sebasdv/redbearpad-pcb/firmware/redbearpad_xinput/redbearpad_xinput.ino

/*
 * RedBearPad v2 - XInput (mando Xbox 360) de 12 botones, sin OLED.
 * Placa de compilacion: "Arduino Micro w/ XInput" (FQBN xinput:avr:micro).
 * Sin serial (XInput no es CDC): LED 13 parpadea como "vivo".
 * Reflasheo: doble-reset manual para entrar al bootloader.
 *
 * Mapeo (contrato PCB v2). PIN_BOTON en orden de indice fisico:
 *   0:Arriba(D3,SW1) 1:Abajo(D1,SW2) 2:Izq(D2,SW3) 3:Der(D0,SW4)
 *   4:SW5(D11) 5:SW6(D12) 6:SW7(A0) 7:SW8(A1)
 *   8:L(D8,SW9) 9:R(D9,SW10) 10:Select(D5,SW11) 11:Start(D10,SW12)
 *
 * Los 4 botones de cara son un cuadrado 2x2 en la mitad derecha de la placa:
 *   SW5 arriba-izq  SW6 arriba-der
 *   SW7 abajo-izq   SW8 abajo-der
 * Se asignan como el diamante Xbox girado 45 grados, de modo que se cumplan las
 * cuatro relaciones de la convencion: Y arriba, A abajo, X izquierda, B derecha.
 *   X Y
 *   A B
 */
#include <XInput.h>

const uint8_t NUM_BOTONES = 12;
const uint8_t PIN_BOTON[NUM_BOTONES] = { 3, 1, 2, 0, 11, 12, A0, A1, 8, 9, 5, 10 };
const uint8_t IDX_UP = 0, IDX_DOWN = 1, IDX_LEFT = 2, IDX_RIGHT = 3;

bool estadoPrev[NUM_BOTONES];
uint8_t integrador[NUM_BOTONES];
uint32_t tUltimoSample = 0;
const uint8_t SAMPLE_MS = 1;
const uint8_t INTEGRADOR_MAX = 12;

void setup() {
  // --- TEST OVERCLOCK: baja el CPU a 8 MHz (en spec) sin tocar el PLL del USB ---
  // El 32U4 a 16 MHz @ 3.3V esta fuera de spec y glitchea al calentar (botones vecinos
  // se acoplan tras ~5 min). El USB se clockea del PLL (independiente del prescaler
  // CLKPR), asi que el mando sigue enumerando como Xbox, pero el CPU pasa a 8 MHz y
  // digitalRead deja de fallar.
  // OJO (temporal): millis()/timing corren a la mitad -> heartbeat ~0.5 Hz, muestreo
  // ~2 ms, debounce ~24 ms. Si el bounce desaparece, se hace variant 8 MHz definitivo.
  CLKPR = 0x80;   // habilita el cambio de prescaler (hay 4 ciclos para el 2do write)
  CLKPR = 0x01;   // prescaler /2 -> CPU 8 MHz

  for (uint8_t i = 0; i < NUM_BOTONES; i++) {
    pinMode(PIN_BOTON[i], INPUT_PULLUP);
    estadoPrev[i] = false;
    integrador[i] = 0;
  }
  pinMode(LED_BUILTIN, OUTPUT);
  XInput.setAutoSend(false);
  XInput.begin();
}

void loop() {
  uint32_t ahora = millis();
  bool huboCambio = false;

  if (ahora - tUltimoSample >= SAMPLE_MS) {
    tUltimoSample = ahora;
    for (uint8_t i = 0; i < NUM_BOTONES; i++) {
      bool leido = (digitalRead(PIN_BOTON[i]) == LOW);
      if (leido) { if (integrador[i] < INTEGRADOR_MAX) integrador[i]++; }
      else       { if (integrador[i] > 0)              integrador[i]--; }
      bool nuevo = estadoPrev[i];
      if (integrador[i] >= INTEGRADOR_MAX) nuevo = true;
      else if (integrador[i] == 0)         nuevo = false;
      if (nuevo != estadoPrev[i]) { estadoPrev[i] = nuevo; huboCambio = true; }
    }
  }

  if (huboCambio) {
    bool up = estadoPrev[IDX_UP], down = estadoPrev[IDX_DOWN];
    bool left = estadoPrev[IDX_LEFT], right = estadoPrev[IDX_RIGHT];
    XInput.setJoystick(JOY_LEFT, up, down, left, right);
    XInput.setDpad(up, down, left, right);
    XInput.setButton(BUTTON_X,     estadoPrev[4]);   // SW5 arriba-izq
    XInput.setButton(BUTTON_Y,     estadoPrev[5]);   // SW6 arriba-der
    XInput.setButton(BUTTON_A,     estadoPrev[6]);   // SW7 abajo-izq
    XInput.setButton(BUTTON_B,     estadoPrev[7]);   // SW8 abajo-der
    XInput.setButton(BUTTON_LB,    estadoPrev[8]);
    XInput.setButton(BUTTON_RB,    estadoPrev[9]);
    XInput.setButton(BUTTON_BACK,  estadoPrev[10]);
    XInput.setButton(BUTTON_START, estadoPrev[11]);
    XInput.send();
  }

  digitalWrite(LED_BUILTIN, (millis() / 500) % 2);
}
